eguerreropen/Rover-HandsOn/CAD's/Mecanismos/Brazo levantador.SLDPRT

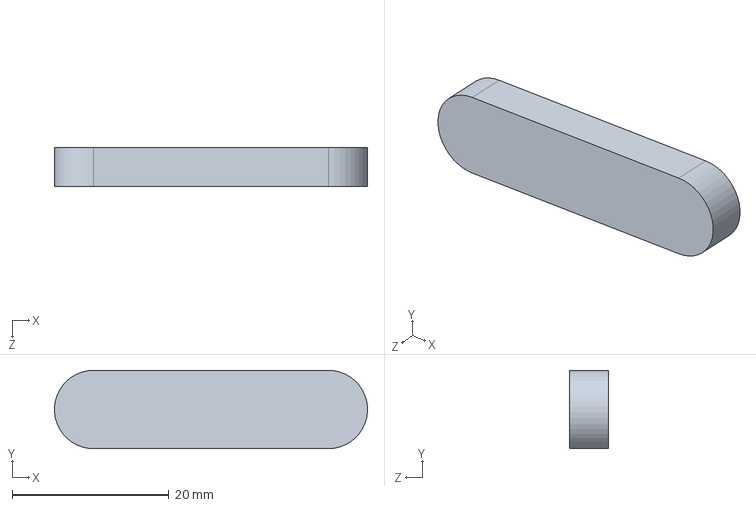
[picture p19: CAD file, 2026-03-27, last stored version]
CAD's/Mecanismos/Brazo levantador.SLDPRT
40.0 x 10.0 x 5.00 mm
